enochchau/dropout-numpad/graphics/build_guide/2_capacitors _2.jpg

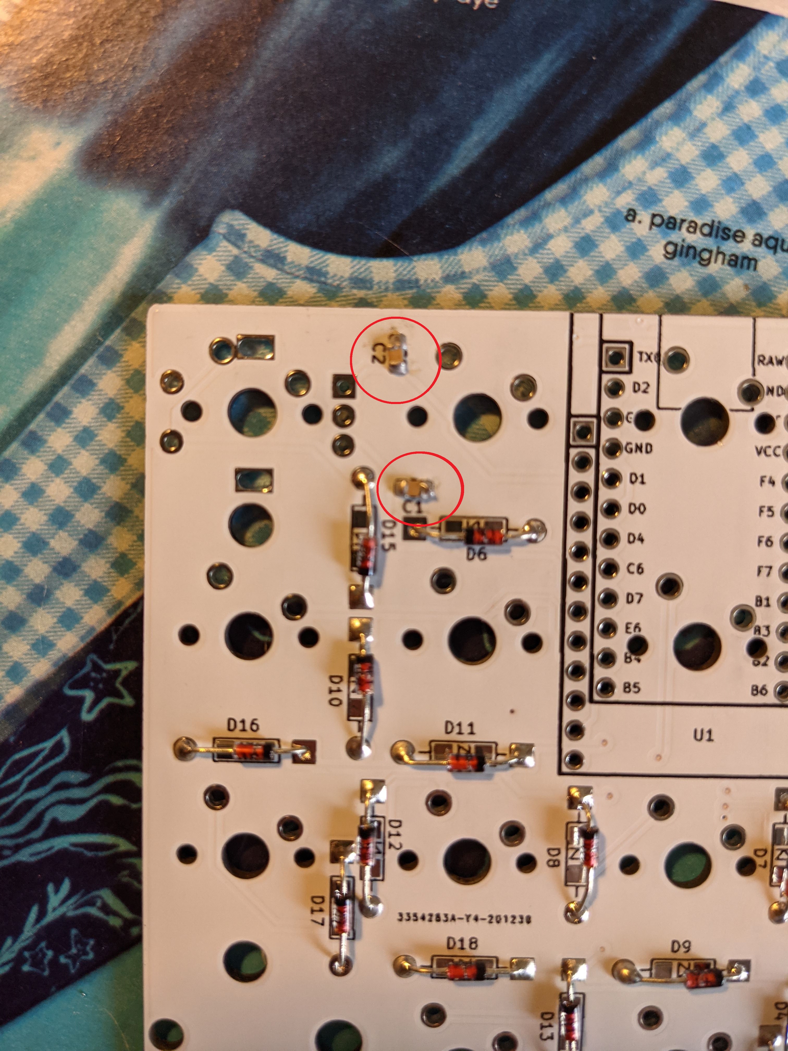
graphics/build_guide/2_capacitors _2.jpg
